HBBisenieks/jackalope_keyboard/case/jackalope_1p_minimal_bottom.dxf

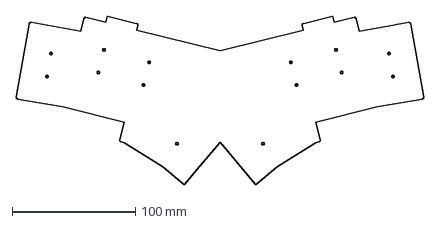
[picture p22: CAD file, 2022-03-13]
case/jackalope_1p_minimal_bottom.dxf
330.3 x 136.5 mm
