HBBisenieks/jackalope_keyboard/case/split_case_minimal_plate_3d.stl

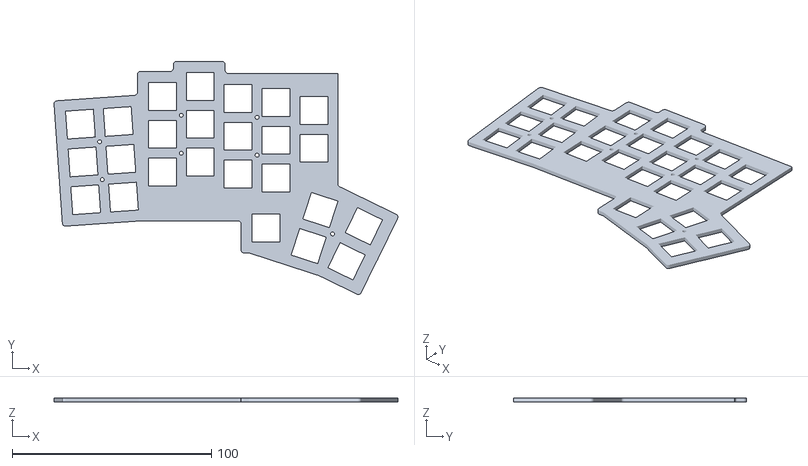
[picture p23: CAD file, 2022-03-13]
case/split_case_minimal_plate_3d.stl
172.5 x 116.9 x 2.00
